prydin/the-bog-standard/spice/class_ab-gate-driver-pnp-ltp.asc

B1: bv; v=if(time>1e-6,{a}*sgn(v(sine)),0)
B2: bv; V=if({square}>0,v(sqr),v(sine))
C1: cap; 220p
C2: cap; 4.7µ
C3: cap; 1; 4.7µ
C4: cap; 1; 220µ
C5: cap; 4.7µ
C6: cap; 47p
C7: cap; 10µ
C8: cap; 47p
C9: cap; 47p
C10: cap; 220n
C15: cap; 100n
C115: cap; 500µ
C207: cap; 159.2n
C208: cap; 79.62n
C209: cap; 79.62n
C310: cap; 7m
C312: cap; 7m
C318: cap; 200µ
C319: cap; 200µ
D1: diode; 1N4148
D2: diode; 1N4148
D3: diode; 1N4148
D4: zener; UMZ5_1N
D5: diode; 1N4148
D6: zener; UMZ5_1N
D7: diode; 1N4148
E24: res; 10
L3: ind; 1m
L104: ind; 20m
Q1: pnp; 2N5401
Q2: pnp; 2N5401
Q3: npn; 2N5550
Q4: pnp; 2N5401
Q5: npn; 2N5550
Q6: pnp; 2N5401
Q7: npn; 2N5550
Q8: npn; 2N5550
Q9: pnp; 2N5401
Q10: pnp; BD140C
Q11: npn; BD139C
Q12: npn; BD139C
Q13: npn; BD139C
Q14: pnp; BD140C
Q15: nmos; IRFP240
Q16: pmos; IRFP9240
R1: res; 1k
R3: res; 470
R4: res; 22k
R5: res; 4.7k
R6: res; 4.7k
R7: res; 100
R8: res; 100
R9: res; 470
R10: res; 100
R11: res; 100
R12: res; 1k
R13: res; 1k
R14: res; 22k
R15: res; 4.7k
R16: res; 4.7k
R17: res; 10k
R18: res; 865
R19: res; 47
R20: res; 33
R21: res; 680
R22: res; 56
R23: res; 56
R30: res; 8
R33: res; {r_vol_hi}
R115: res; 6.8
R122: res; 22
R218: res; 2k
R223: res; 2k
R228: res; 1k
R329: res; 1
R331: res; 1
R404: res; {r_vol_lo}
R405: res; {dc_couple_res}
R406: res; {dc_couple_res}
V1: voltage; 40
V2: voltage; ""; AC 0
V3: voltage; 40
V5: voltage; SINE(0 {a} {f}); AC 1
Named nets: 0, IN, B-, B+, OUT, NEG_IN, FB, SINE, SQR
.param f=1k a=0.8 square=0 sim_time=100m delay=0 dc_coupled=0 r_pot=50k vol=1
.param dc_couple_res=if({dc_coupled}>0,1p,10G)
.param r_vol_hi=1m+(1-vol)*r_pot r_vol_lo=1m+vol*r_pot
.tran 0 {sim_time+delay} {delay} 100n
.four {f} 50 -1 v(out)
.option plotwinsize=0 NoOpiter numdgt=15
; .step param vol list  0.25 0.5 0.75 1
.ac dec 1000 1 10meg
.noise out in dec 1000 1 1meg
Notch filter for time domain distortion test
f - Input frequency
a - Input amplitude
vol - Volume
square - Set to non-zero for square wave input
sim_time - Simulation time (not counting settling delay)
delay - Settling delay. Set to several seconds for accurate THD
dc_coupled = Shorts high value capacitors to allow for quick THD checks
Reactive speaker model
